boyuan99/Borot/Parts/connector_thigh_shank2.stl

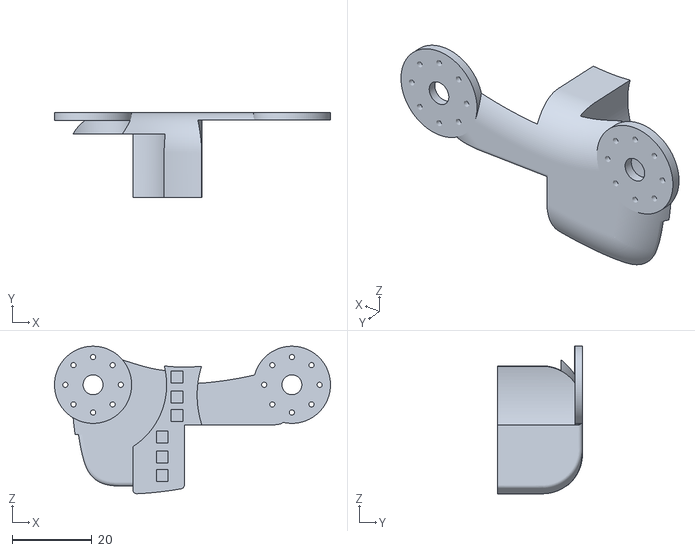
[picture p19: CAD file, 2022-07-09]
Parts/connector_thigh_shank2.stl
69.4 x 21.4 x 37.1
